lab-411/Stemfie-X/img/wheel_02_14_12_1.png

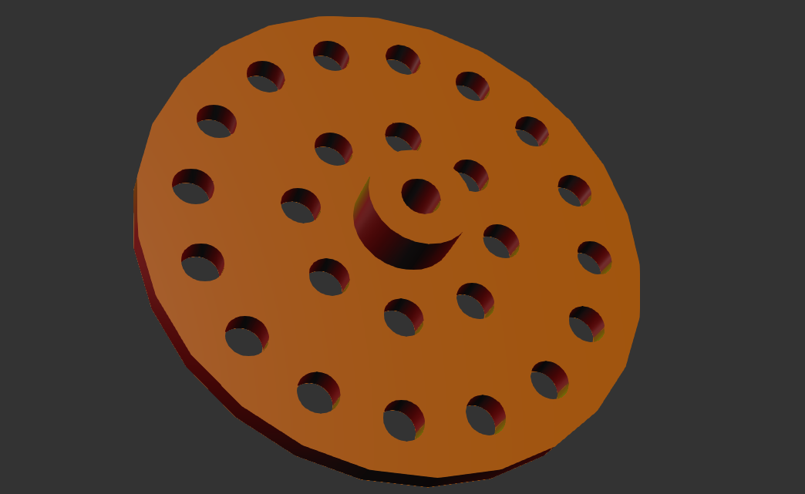
img/wheel_02_14_12_1.png
