lab-411/Stemfie-X/model/0210_most/img/most_06.png

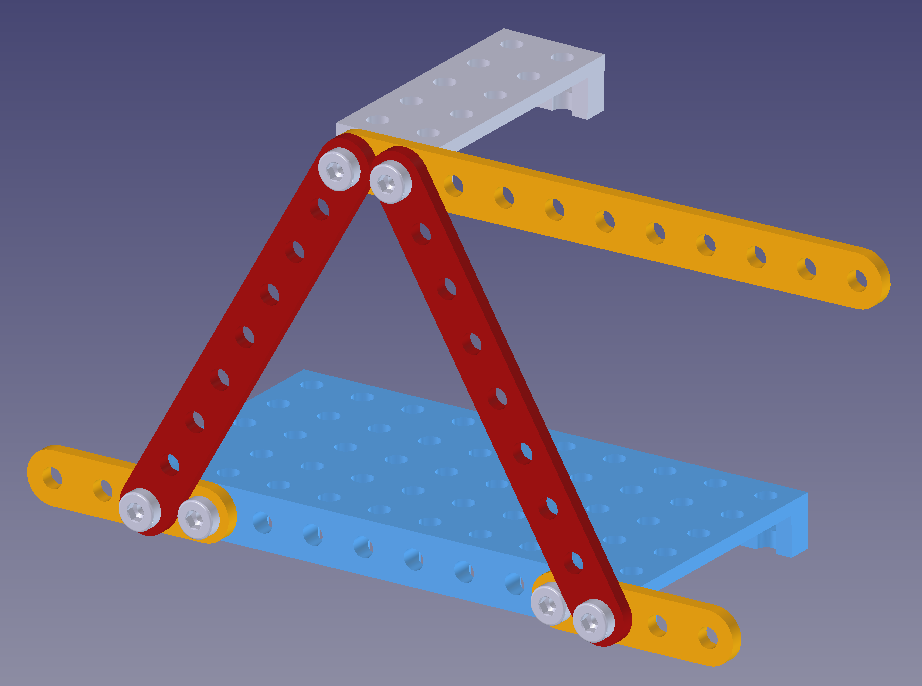
model/0210_most/img/most_06.png
