lab-411/Stemfie-X/model/0212_waren/img/zostava_02.png

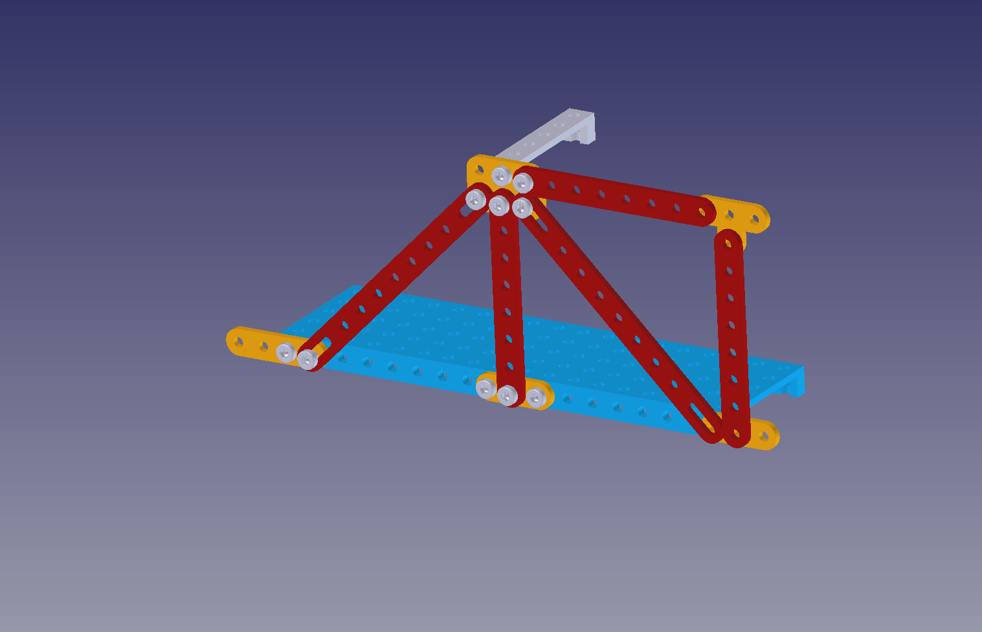
model/0212_waren/img/zostava_02.png
