lab-411/Stemfie-X/model/0215_mini_zeriav/img/2025-12-19_21-37.png

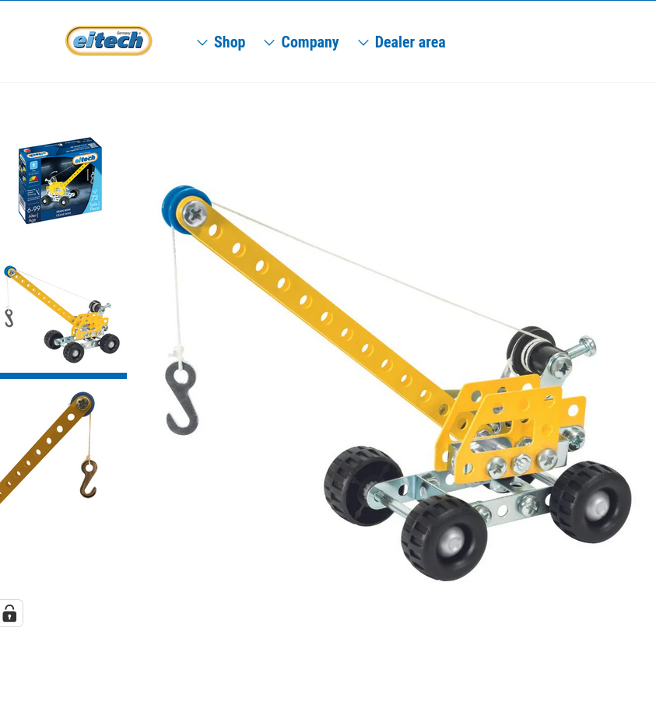
model/0215_mini_zeriav/img/2025-12-19_21-37.png
