lab-411/Stemfie-X/model/0215_mini_zeriav/img/diely_02.jpg

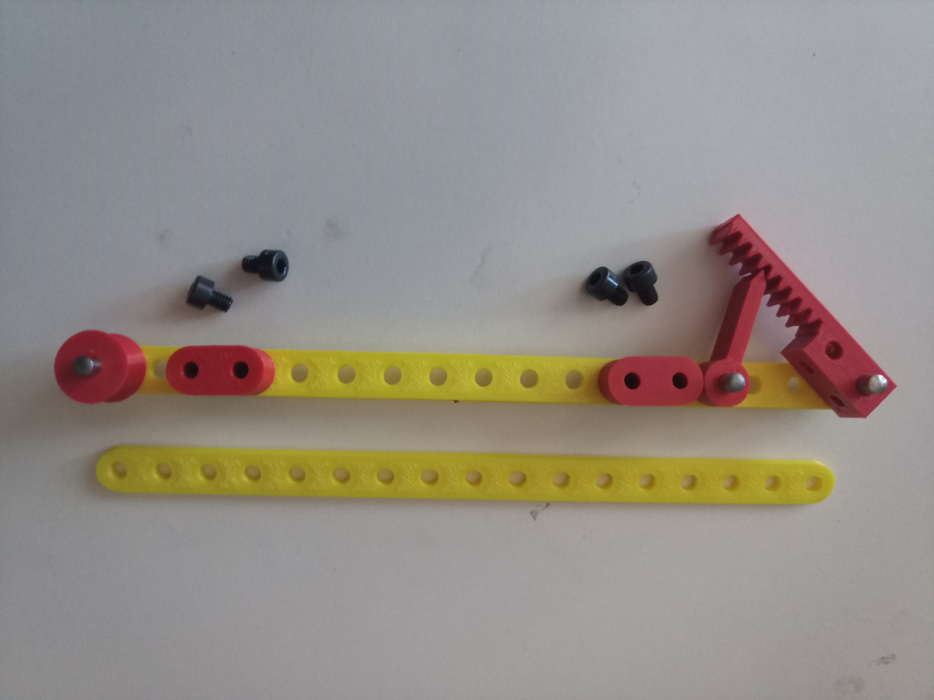
model/0215_mini_zeriav/img/diely_02.jpg
