lab-411/Stemfie-X/model/0215_mini_zeriav/img/IMG_20260729_085818_136.jpg

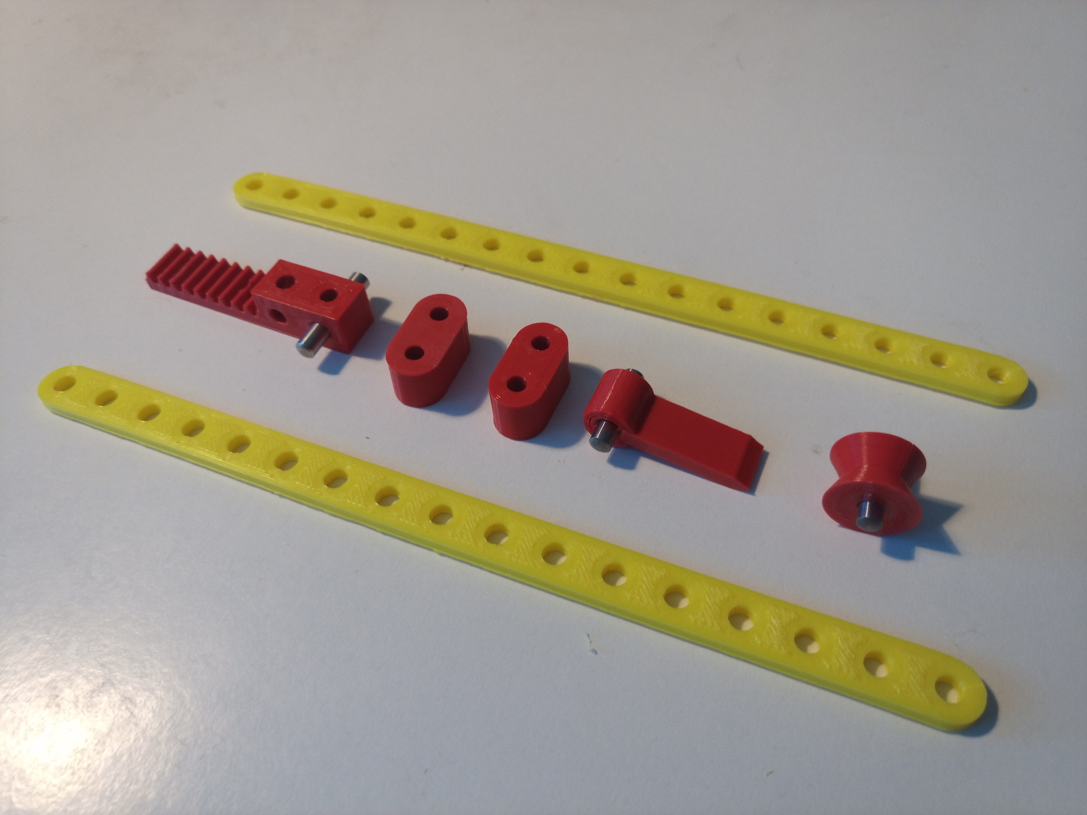
model/0215_mini_zeriav/img/IMG_20260729_085818_136.jpg
