lab-411/Stemfie-X/model/0215_mini_zeriav/img/IMG_20260729_090453_453.jpg

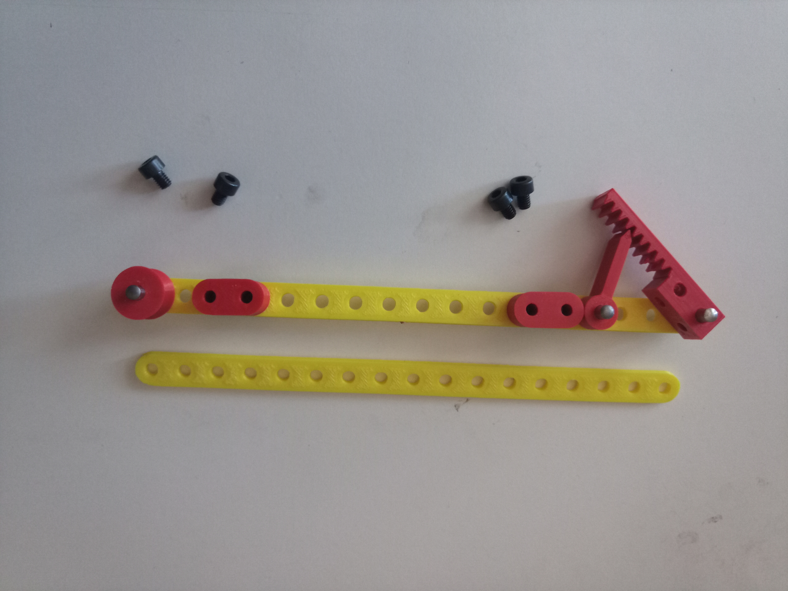
model/0215_mini_zeriav/img/IMG_20260729_090453_453.jpg
