lab-411/Stemfie-X/model/0215_mini_zeriav/img/IMG_20260730_194325_354.jpg

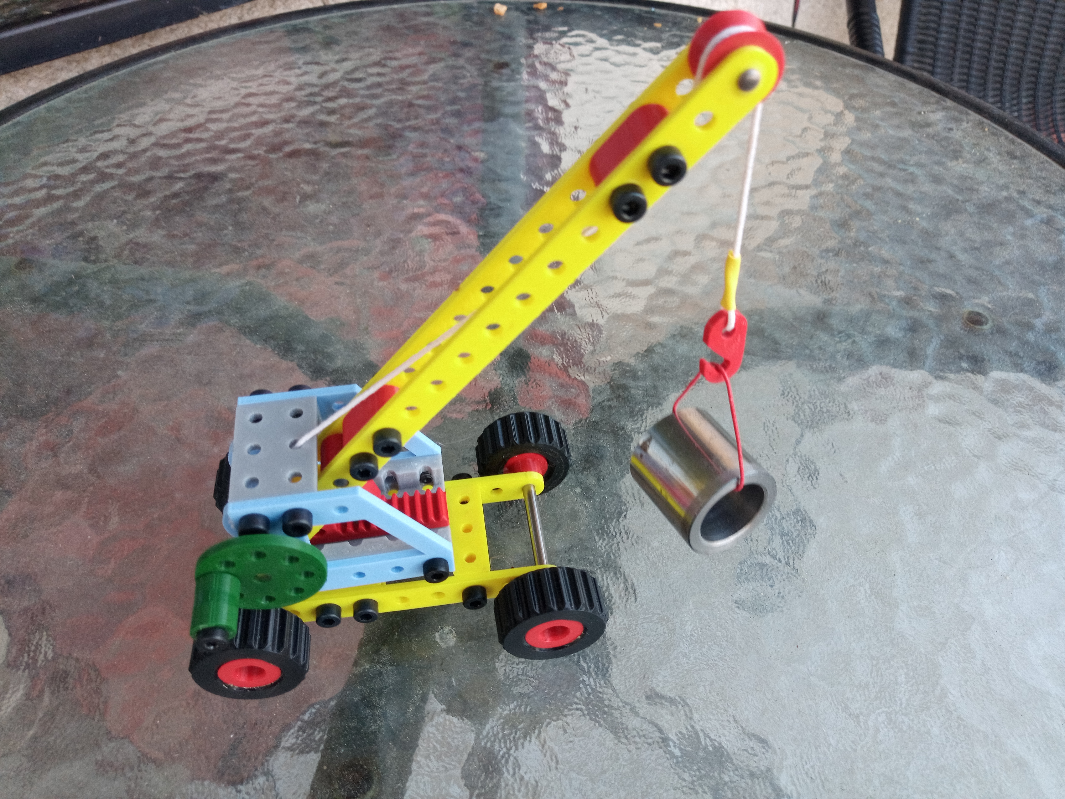
model/0215_mini_zeriav/img/IMG_20260730_194325_354.jpg
