lab-411/Stemfie-X/model/0215_mini_zeriav/img/IMG_20260730_194350_189.jpg

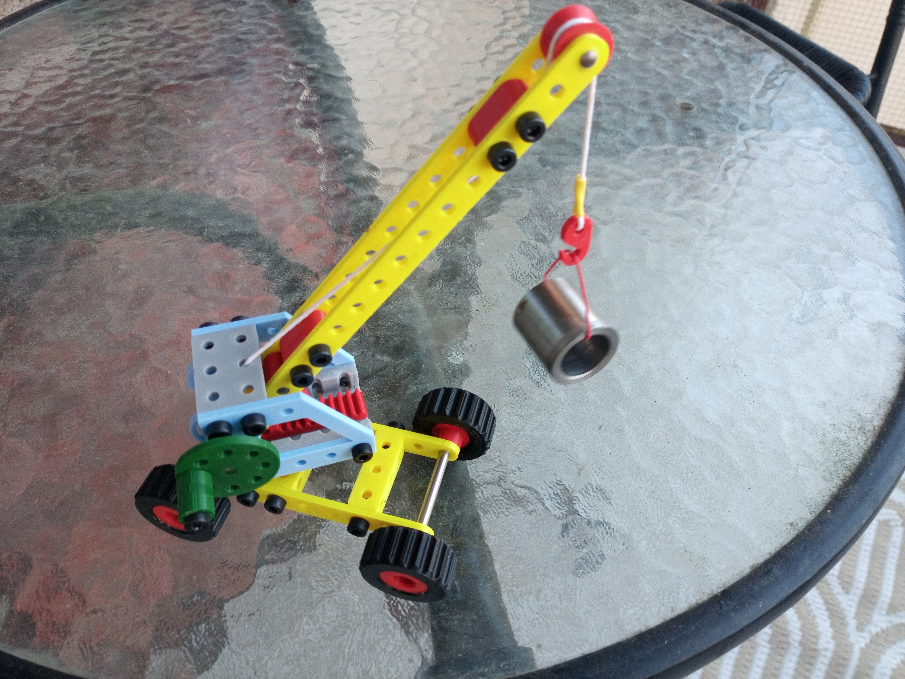
model/0215_mini_zeriav/img/IMG_20260730_194350_189.jpg
