lab-411/Stemfie-X/model/0215_mini_zeriav/img/img_sc_01.png

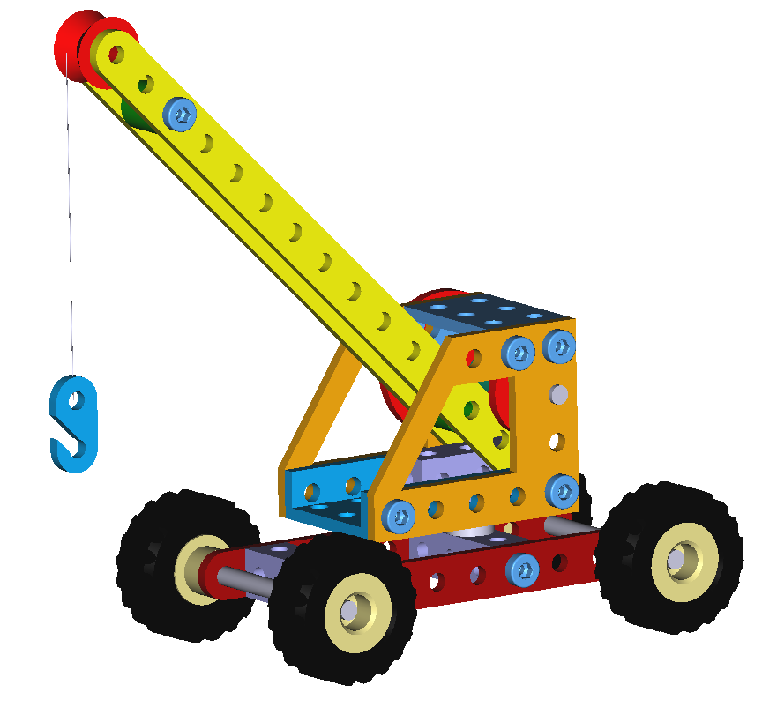
model/0215_mini_zeriav/img/img_sc_01.png
