lab-411/Stemfie-X/model/0215_mini_zeriav/img/img_sc_03.png

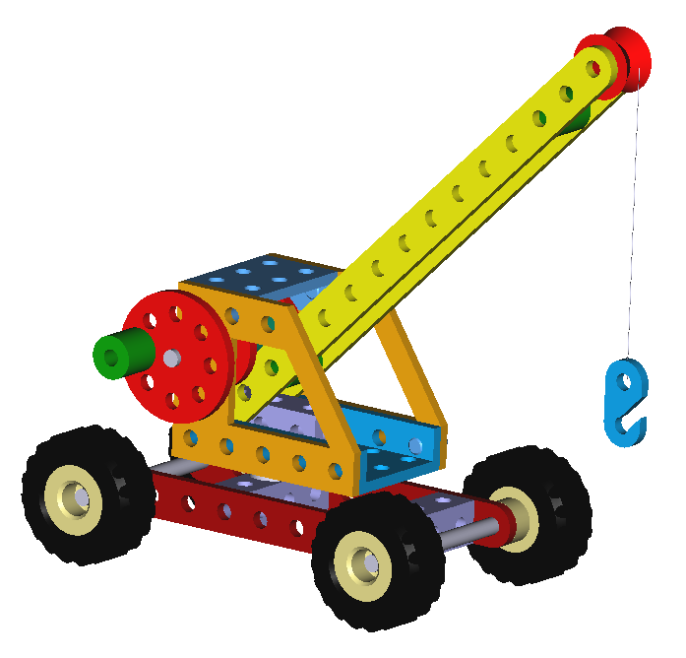
model/0215_mini_zeriav/img/img_sc_03.png
