lab-411/Stemfie-X/model/0215_mini_zeriav/img/img_zeriav_01.jpg

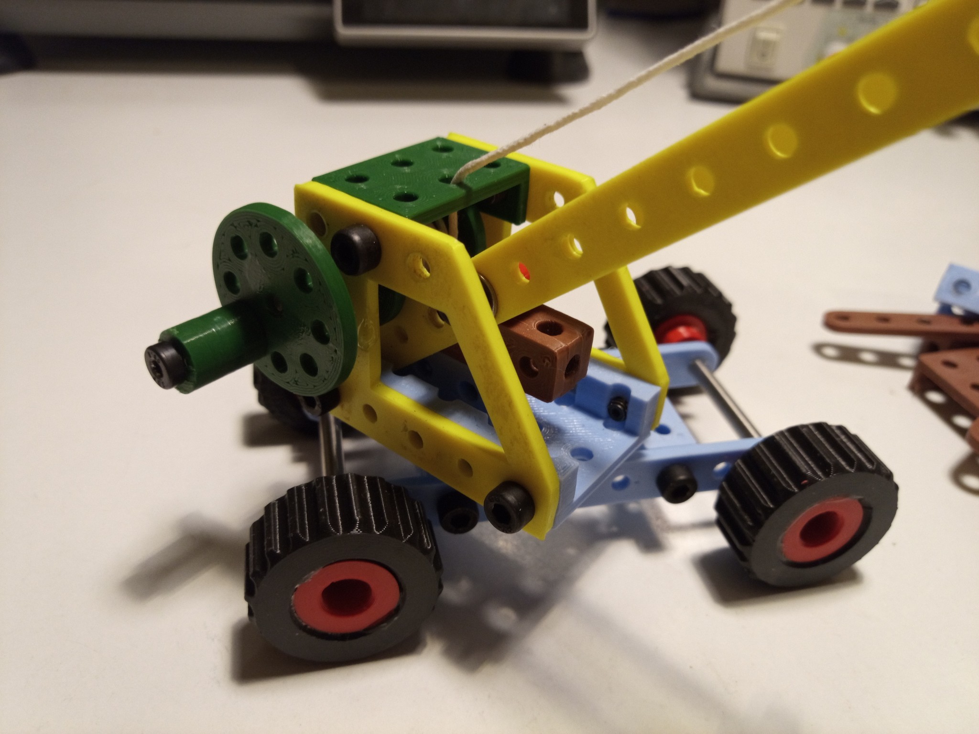
model/0215_mini_zeriav/img/img_zeriav_01.jpg
