lab-411/Stemfie-X/model/0215_mini_zeriav/img/kabina_03.png

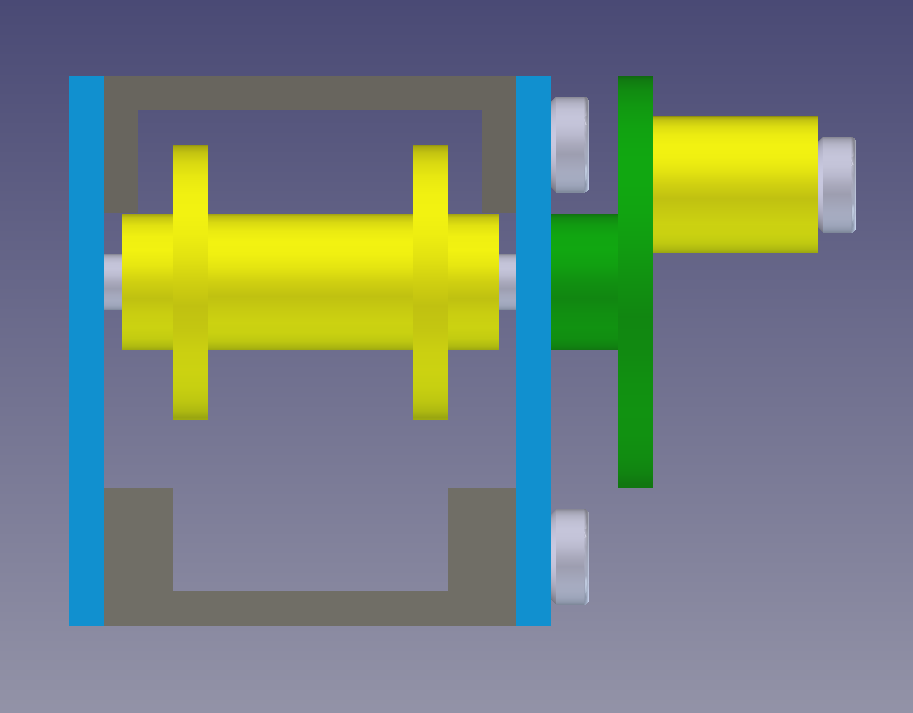
model/0215_mini_zeriav/img/kabina_03.png
