lab-411/Stemfie-X/model/0225_bobcat/img/img_04.png

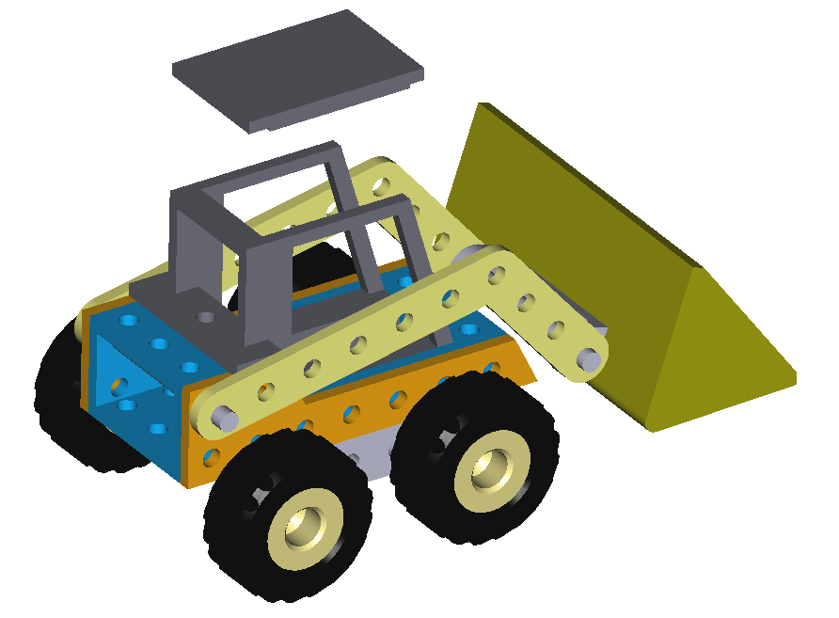
model/0225_bobcat/img/img_04.png
