lab-411/Stemfie-X/model/0225_bobcat_v02/img/IMG_20260118_134334_418.jpg

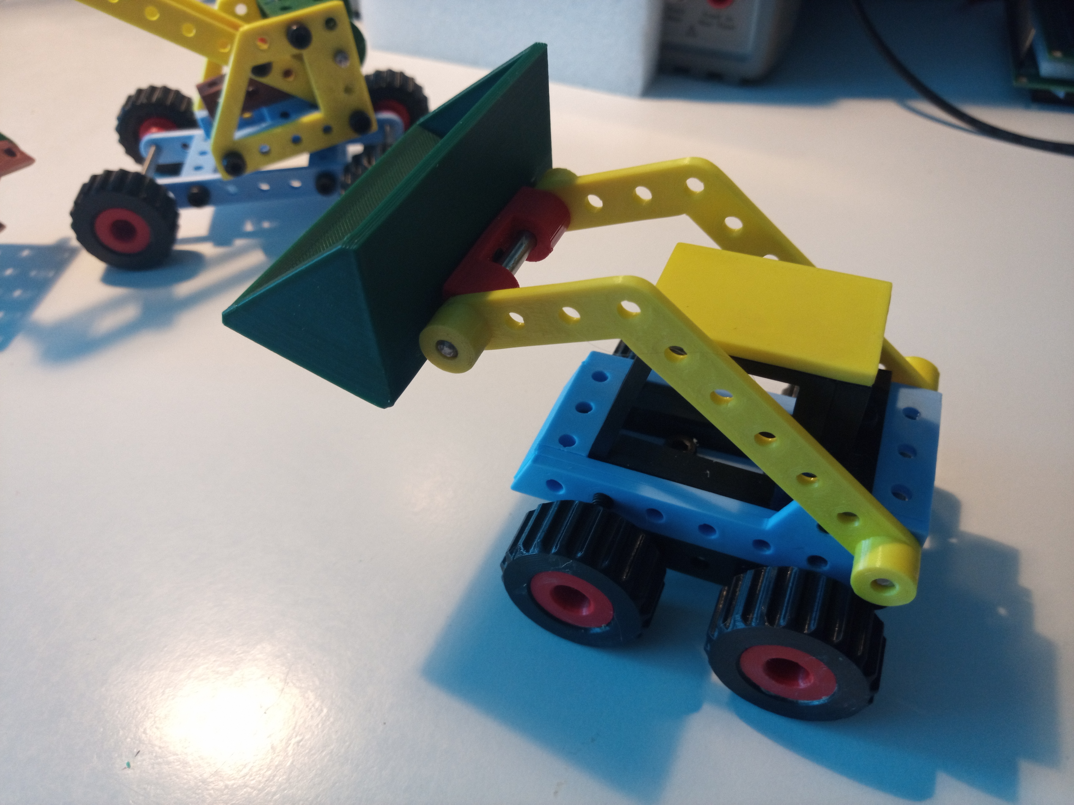
model/0225_bobcat_v02/img/IMG_20260118_134334_418.jpg
