lab-411/Stemfie-X/plantuml/aktivity.png

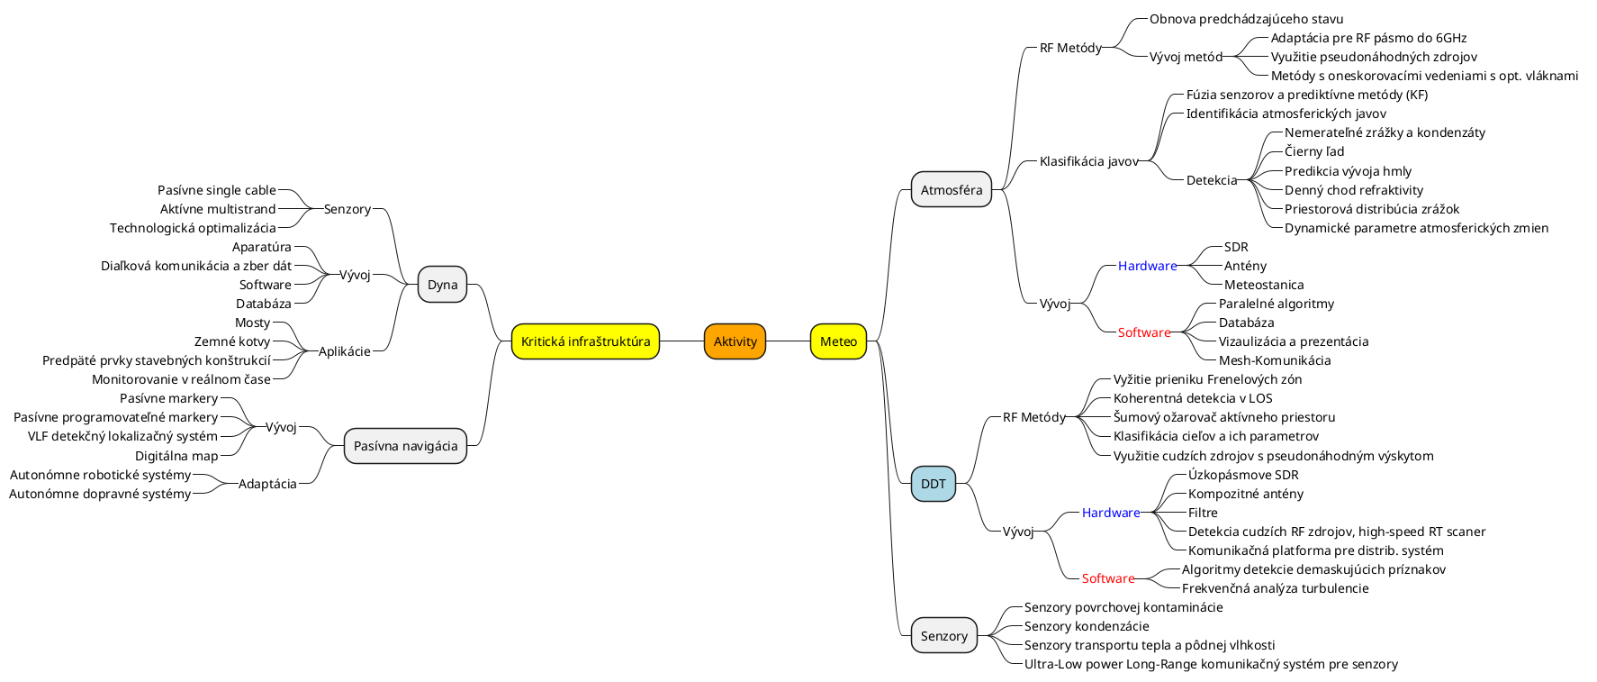
plantuml/aktivity.png
