lab-411/Stemfie-X/plantuml/kompetencie.png

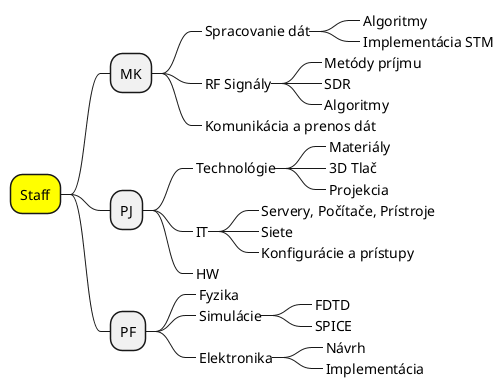
plantuml/kompetencie.png
