lab-411/Stemfie-X/src/0520b.png

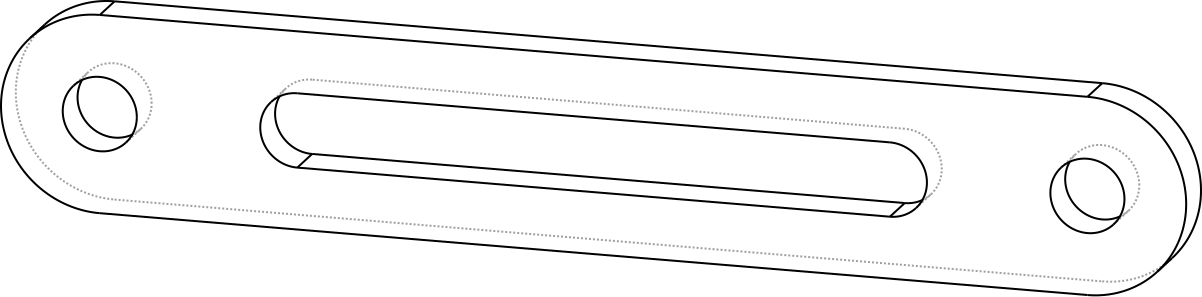
src/0520b.png
