lab-411/Stemfie-X/model/0225_bobcat/parts/user_P_03_24.step

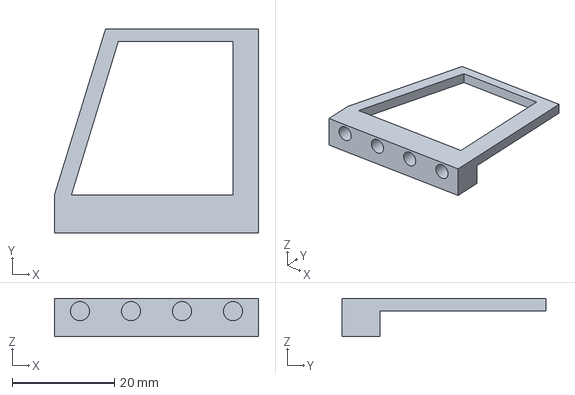
[picture p125: CAD file, 2026-01-18]
model/0225_bobcat/parts/user_P_03_24.step
40.0 x 40.0 x 7.50 mm
