lab-411/Stemfie-X/model/0225_bobcat_v02/parts/block_B_03.step

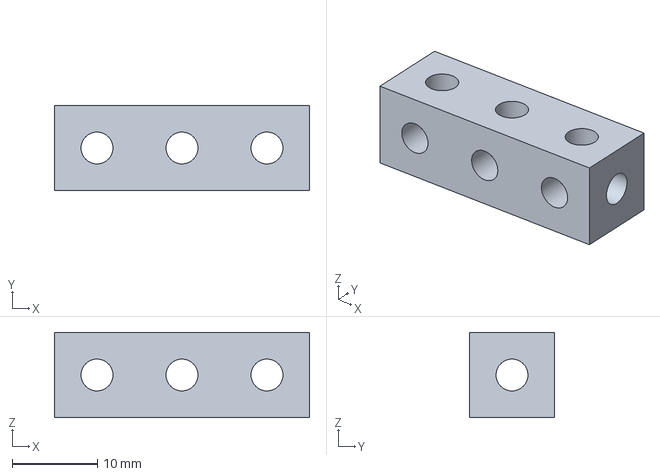
[picture p126: CAD file, 2026-01-18]
model/0225_bobcat_v02/parts/block_B_03.step
30.0 x 10.0 x 10.0 mm
