lab-411/Stemfie-X/model/1020_spirograf/parts/sp_gear_50.step

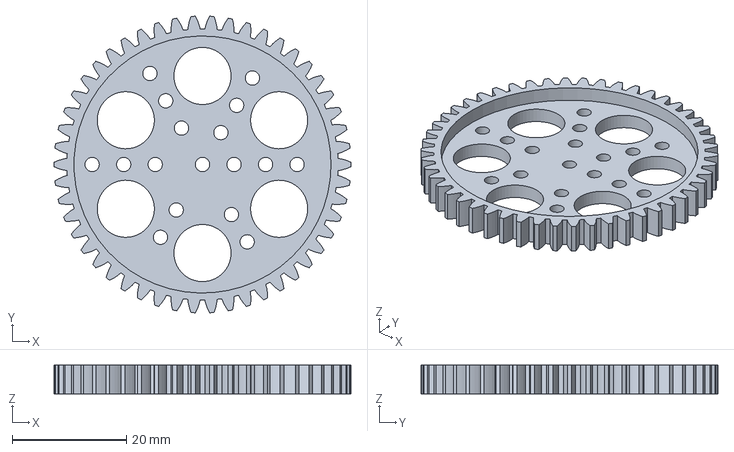
[picture p127: CAD file, 2026-01-18]
model/1020_spirograf/parts/sp_gear_50.step
52.0 x 51.9 x 5.00 mm
