lab-411/Stemfie-X/model/0210_most/parts/block_U_02_05_14_12.step

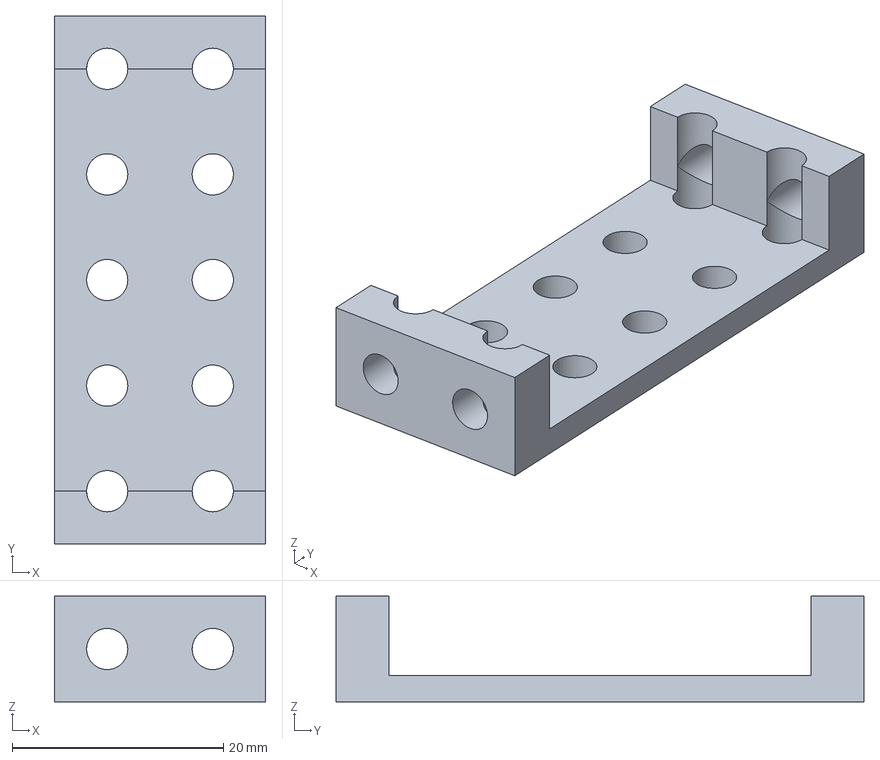
[picture p128: CAD file, 2025-12-20]
model/0210_most/parts/block_U_02_05_14_12.step
20.0 x 50.0 x 10.0 mm
