lab-411/Stemfie-X/model/0215_mini_zeriav/parts/wheel_B_02_14.step

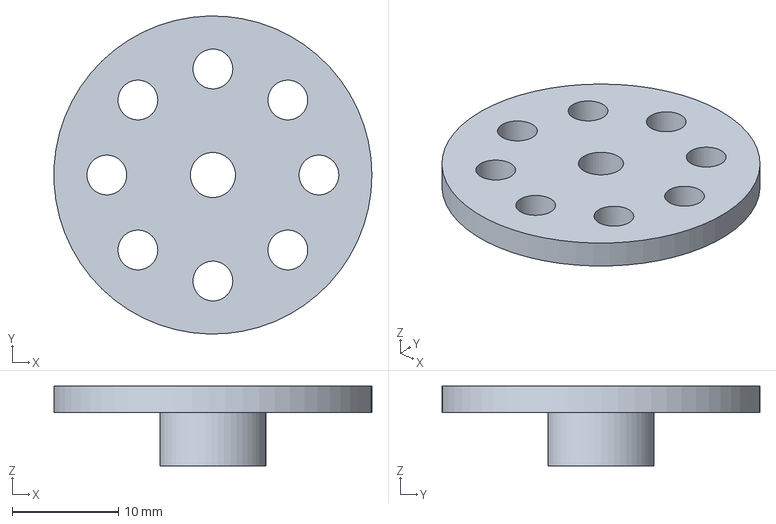
[picture p129: CAD file, 2026-07-30]
model/0215_mini_zeriav/parts/wheel_B_02_14.step
30.0 x 30.0 x 7.50 mm
