lab-411/Stemfie-X/model/0220_maly_mlyn/parts/brace_B_05.step

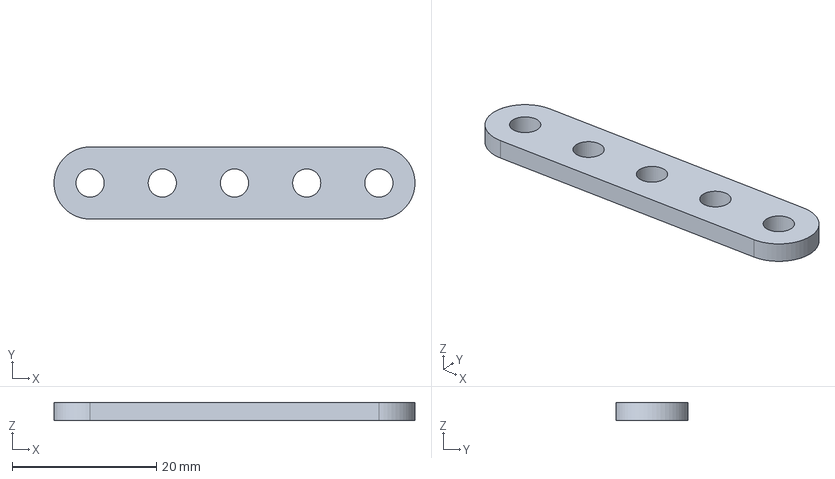
[picture p130: CAD file, 2026-01-04]
model/0220_maly_mlyn/parts/brace_B_05.step
50.0 x 10.0 x 2.50 mm
