lab-411/Stemfie-X/model/0225_bobcat/parts/user_Y_35_01.step

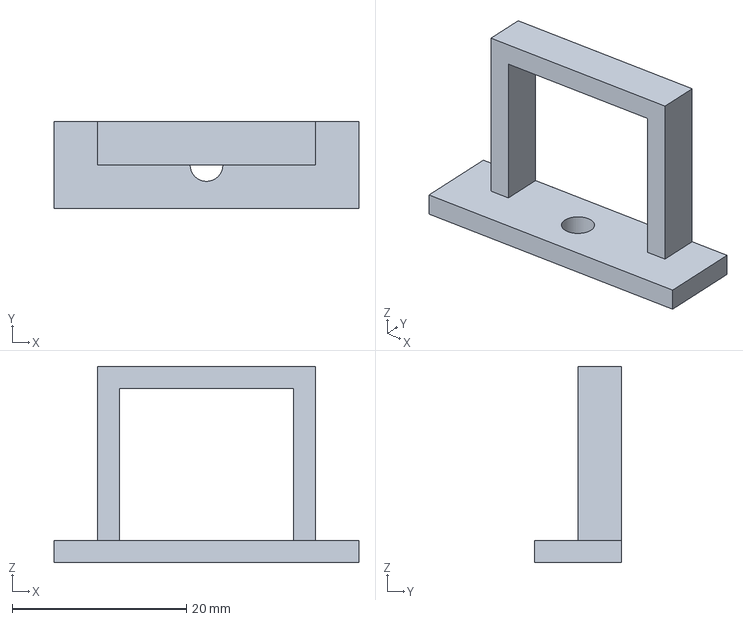
[picture p131: CAD file, 2026-01-18]
model/0225_bobcat/parts/user_Y_35_01.step
35.0 x 10.0 x 22.5 mm
