lab-411/Stemfie-X/model/1020_spirograf/parts/sp_base_90.step

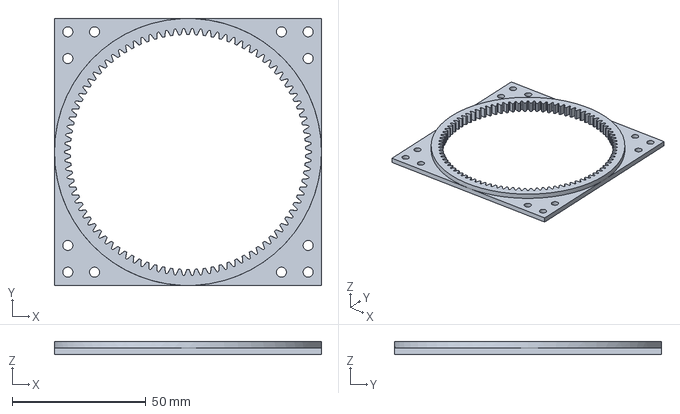
[picture p132: CAD file, 2026-01-18]
model/1020_spirograf/parts/sp_base_90.step
100.0 x 100.0 x 5.00 mm
