lab-411/Stemfie-X/model/0210_most/parts/brace_P_03_02_14.step

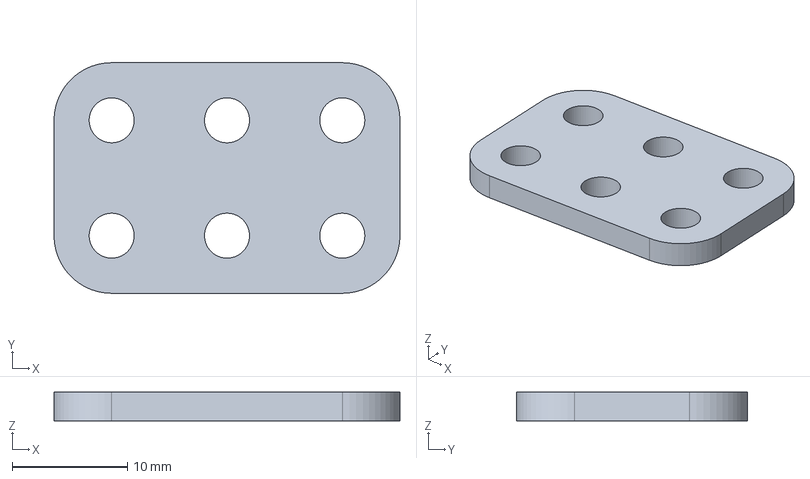
[picture p133: CAD file, 2025-12-20]
model/0210_most/parts/brace_P_03_02_14.step
30.0 x 20.0 x 2.50 mm
