lab-411/Stemfie-X/model/0215_mini_zeriav/parts/rameno.FCStd

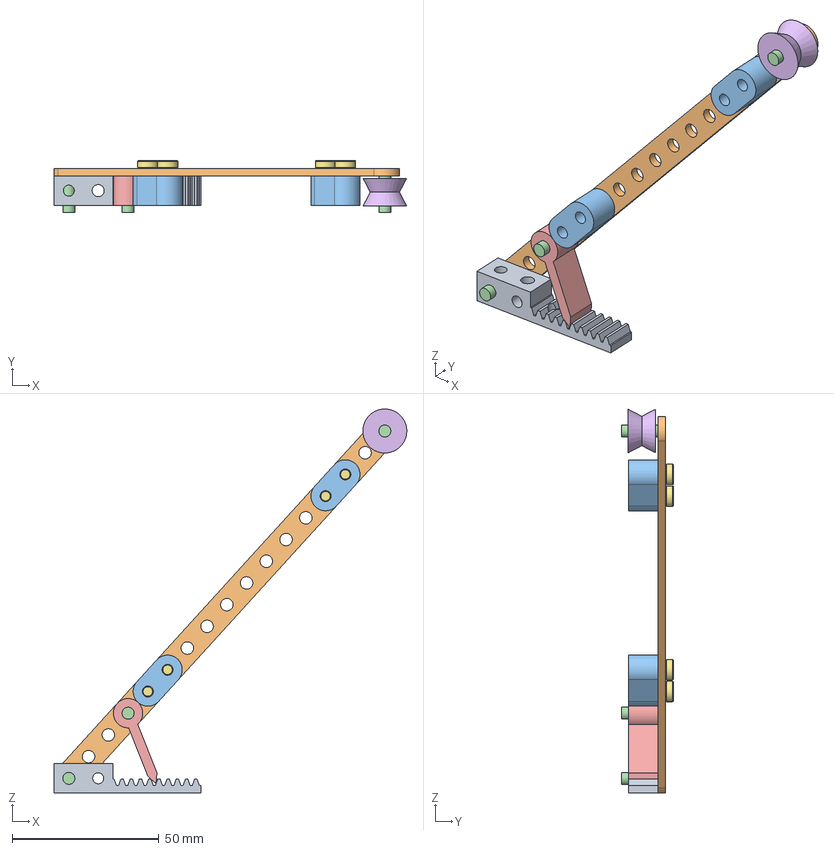
[picture p134: CAD file, 2026-07-30]
model/0215_mini_zeriav/parts/rameno.FCStd
120.2 x 17.8 x 130.8 mm
drziak
rameno
spojka x 2
os_15 x 3
podpera
kladka
M4x6-Screw x 4
