lab-411/Stemfie-X/model/0220_maly_mlyn/parts/brace_B_10.step

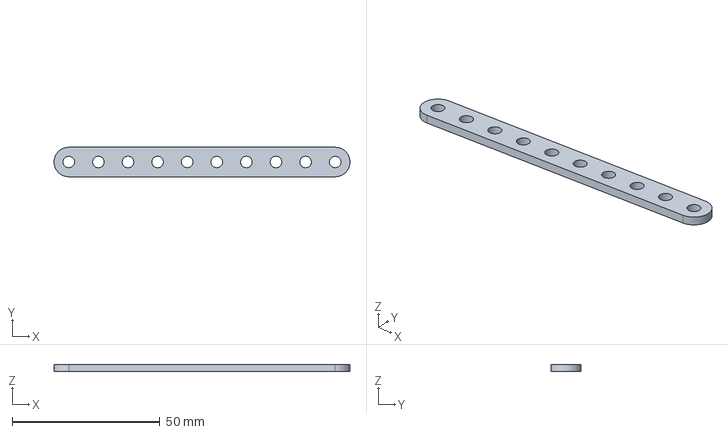
[picture p135: CAD file, 2026-01-04]
model/0220_maly_mlyn/parts/brace_B_10.step
100.0 x 10.0 x 2.50 mm
