lab-411/Stemfie-X/model/0225_bobcat_v02/parts/tire_T_01_03_15.step

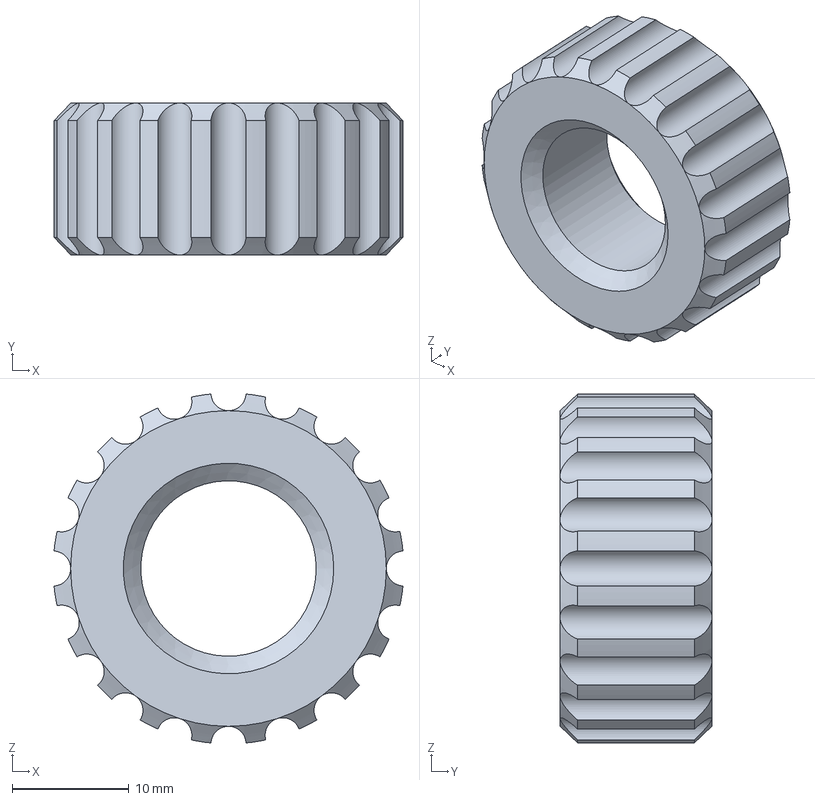
[picture p137: CAD file, 2026-01-18]
model/0225_bobcat_v02/parts/tire_T_01_03_15.step
29.9 x 13.0 x 29.9 mm
