lab-411/Stemfie-X/model/1020_spirograf/parts/sp_gear_65.step

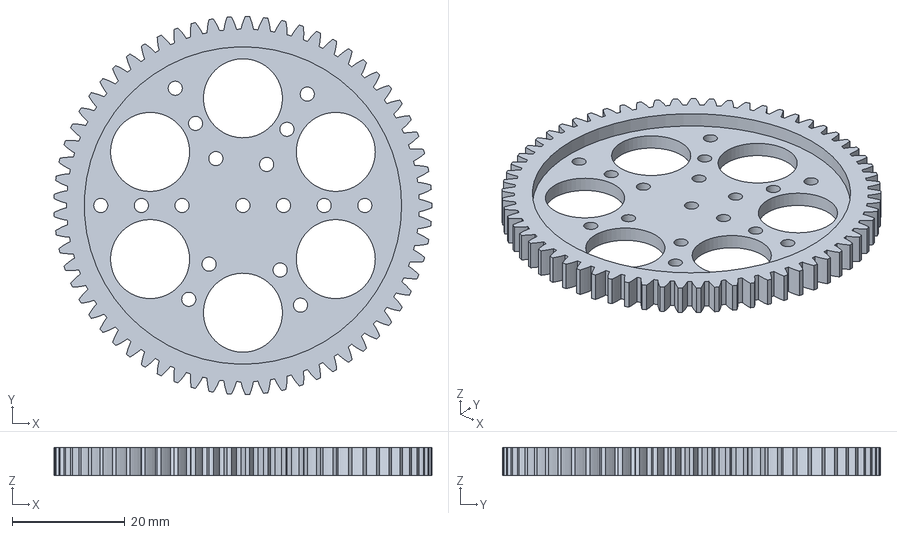
[picture p138: CAD file, 2026-01-18]
model/1020_spirograf/parts/sp_gear_65.step
67.0 x 67.0 x 5.00 mm
