lab-411/Stemfie-X/model/0212_waren/parts/brace_B_03_14.step

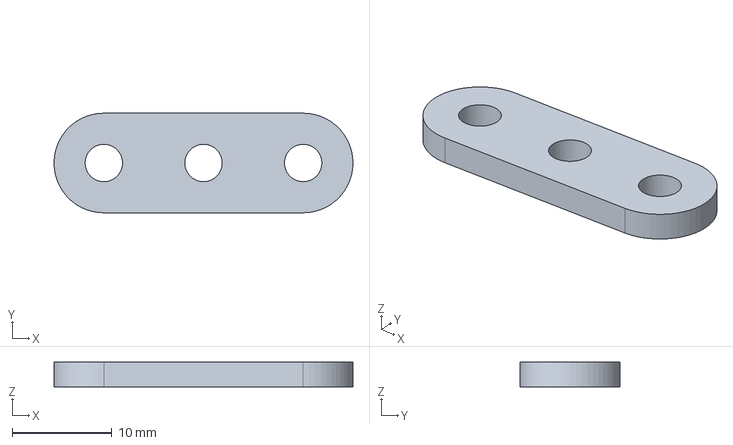
[picture p140: CAD file, 2026-08-03]
model/0212_waren/parts/brace_B_03_14.step
30.0 x 10.0 x 2.50 mm
