lab-411/Stemfie-X/model/0215_mini_zeriav/parts/rack_2.step

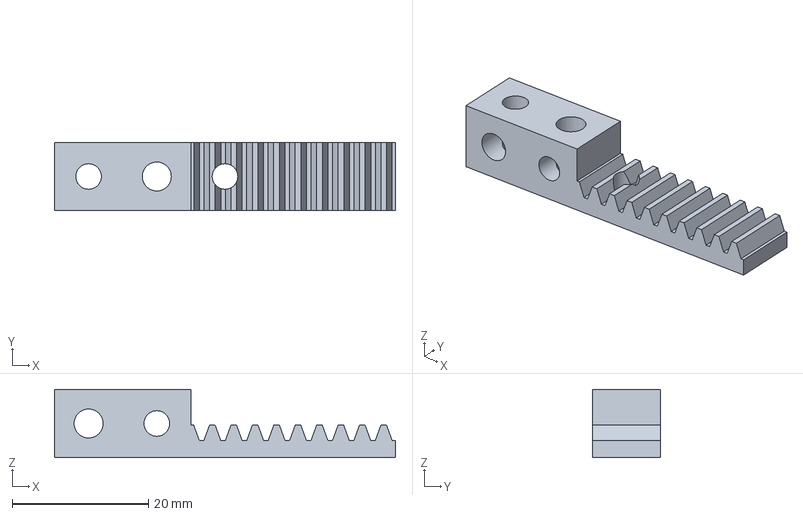
[picture p141: CAD file, 2026-07-30]
model/0215_mini_zeriav/parts/rack_2.step
50.0 x 10.0 x 10.0 mm
