lab-411/Stemfie-X/model/0220_maly_mlyn/parts/brace_A_03_14_06_112.step

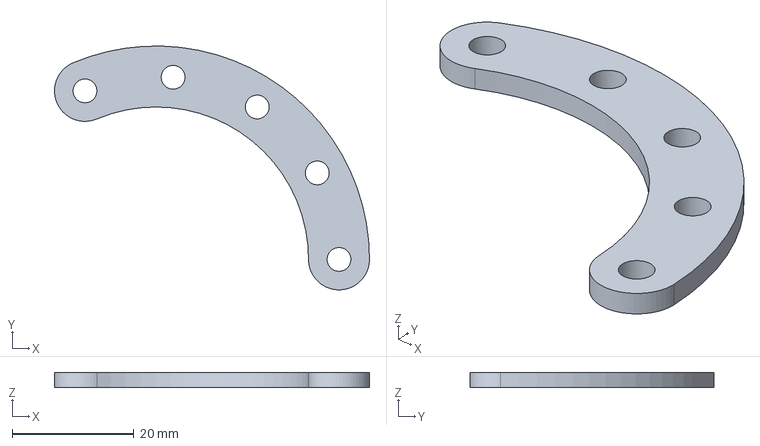
[picture p142: CAD file, 2026-01-04]
model/0220_maly_mlyn/parts/brace_A_03_14_06_112.step
51.7 x 40.0 x 2.50 mm
