lab-411/Stemfie-X/model/0225_bobcat_v02/parts/user_X_35_01.step

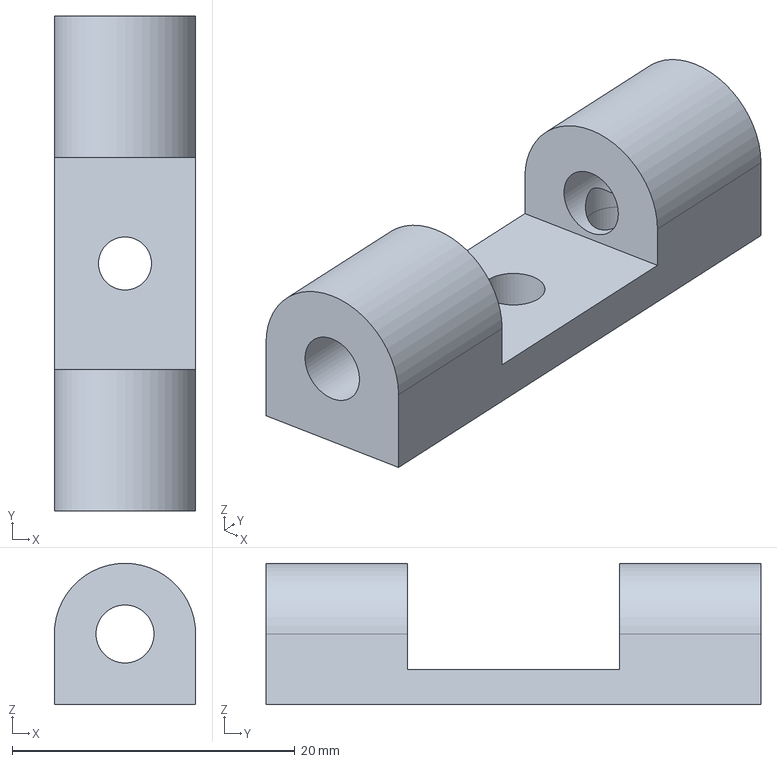
[picture p143: CAD file, 2026-01-18]
model/0225_bobcat_v02/parts/user_X_35_01.step
10.0 x 35.0 x 10.0 mm
