lab-411/Stemfie-X/model/0210_most/parts/brace_B_09_14.step

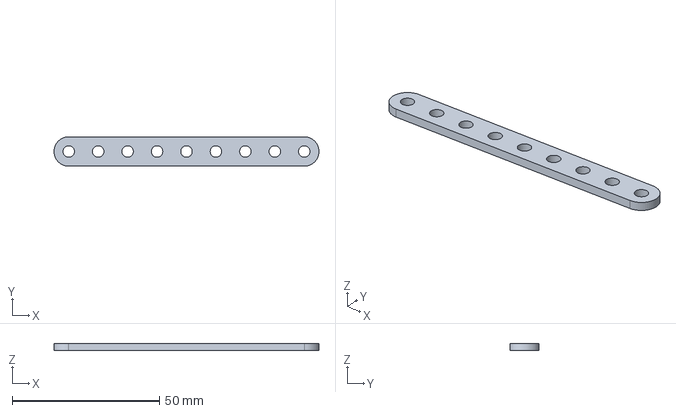
[picture p144: CAD file, 2025-12-20]
model/0210_most/parts/brace_B_09_14.step
90.0 x 10.0 x 2.50 mm
