lab-411/Stemfie-X/model/0215_mini_zeriav/parts/wheel_A_15_14.step

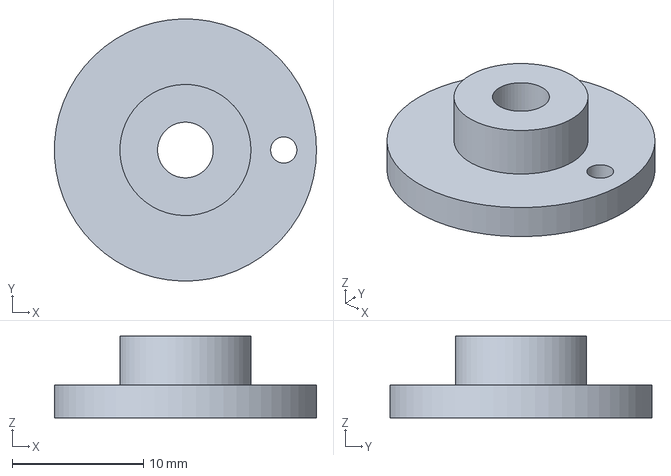
[picture p145: CAD file, 2026-07-30]
model/0215_mini_zeriav/parts/wheel_A_15_14.step
20.0 x 20.0 x 6.25 mm
