lab-411/Stemfie-X/model/0220_maly_mlyn/parts/wheel_B_12_12.step

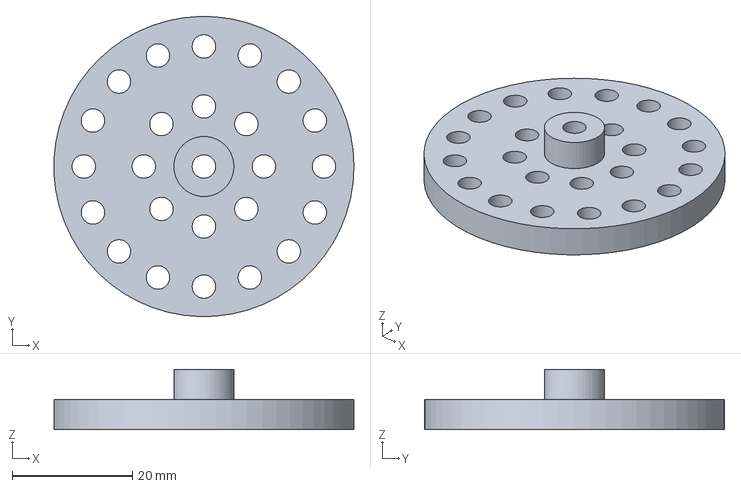
[picture p146: CAD file, 2026-01-04]
model/0220_maly_mlyn/parts/wheel_B_12_12.step
50.0 x 50.0 x 10.0 mm
