lab-411/Stemfie-X/model/0212_waren/parts/brace_T_03_02.step

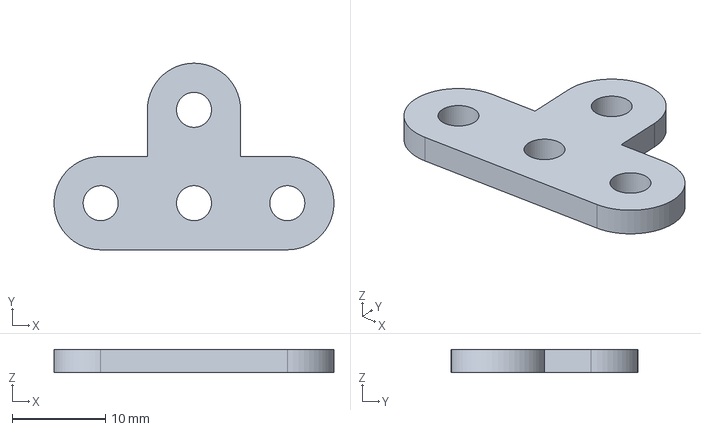
[picture p147: CAD file, 2026-08-03]
model/0212_waren/parts/brace_T_03_02.step
30.0 x 20.0 x 2.50 mm
