lab-411/Stemfie-X/model/0215_mini_zeriav/parts/axis_5.step

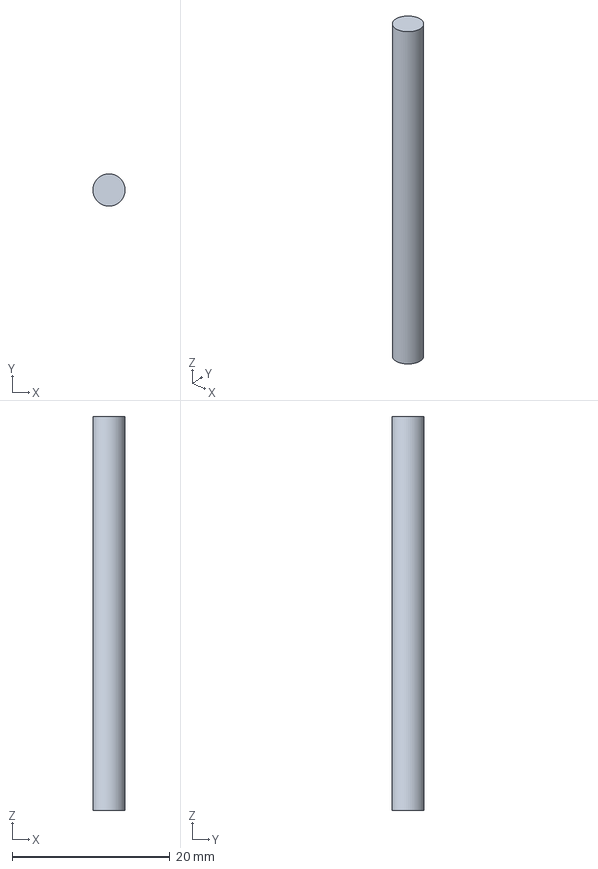
[picture p148: CAD file, 2026-07-30]
model/0215_mini_zeriav/parts/axis_5.step
4.10 x 4.10 x 50.0 mm
