lab-411/Stemfie-X/model/0220_maly_mlyn/parts/pull_B_12.step

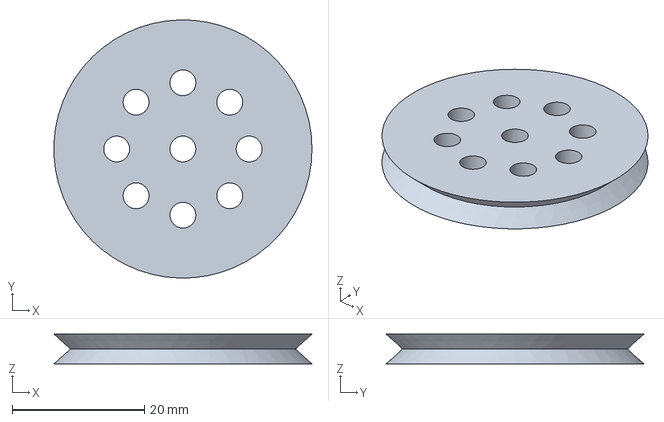
[picture p149: CAD file, 2026-01-04]
model/0220_maly_mlyn/parts/pull_B_12.step
39.0 x 39.0 x 4.50 mm
