lab-411/Stemfie-X/model/0212_waren/parts/block_H_05_05_14_12_02_02.step

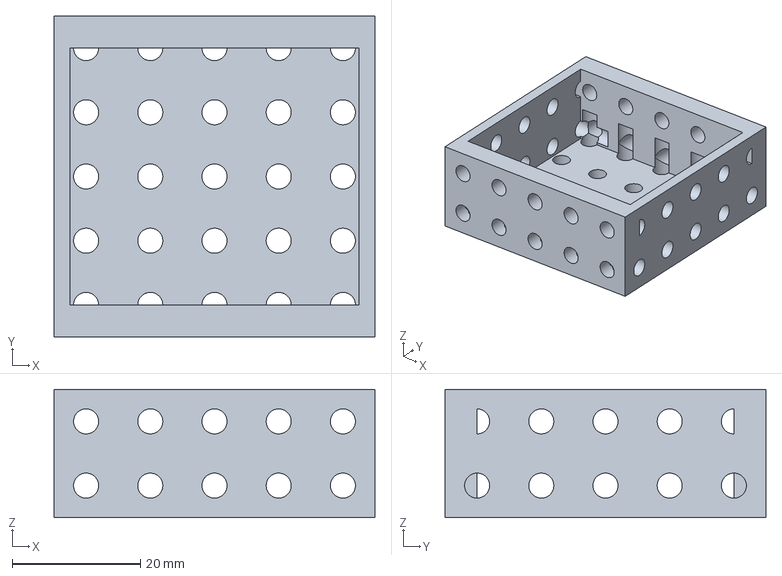
[picture p150: CAD file, 2025-12-20]
model/0212_waren/parts/block_H_05_05_14_12_02_02.step
50.0 x 50.0 x 20.0 mm
