lab-411/Stemfie-X/model/0215_mini_zeriav/parts/base_C_01_15.step

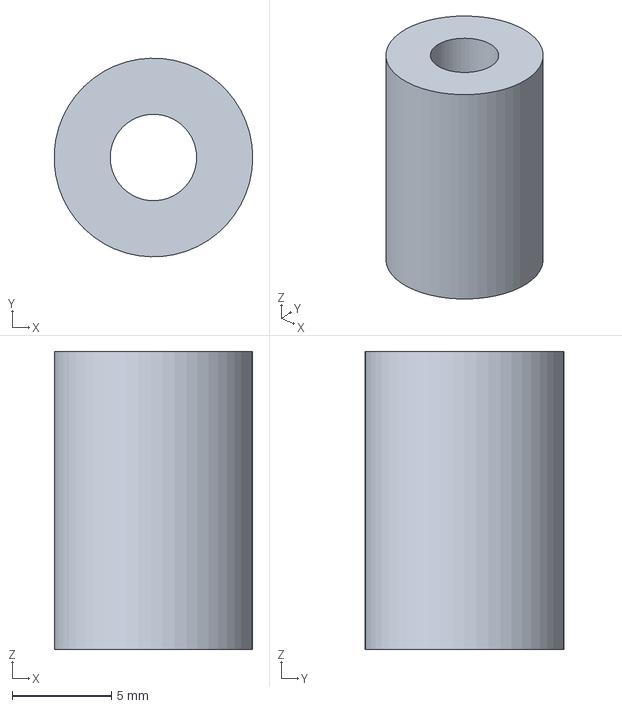
[picture p151: CAD file, 2026-07-30]
model/0215_mini_zeriav/parts/base_C_01_15.step
9.99 x 10.00 x 15.0 mm
