lab-411/Stemfie-X/model/0225_bobcat/parts/user_S_20_40.step

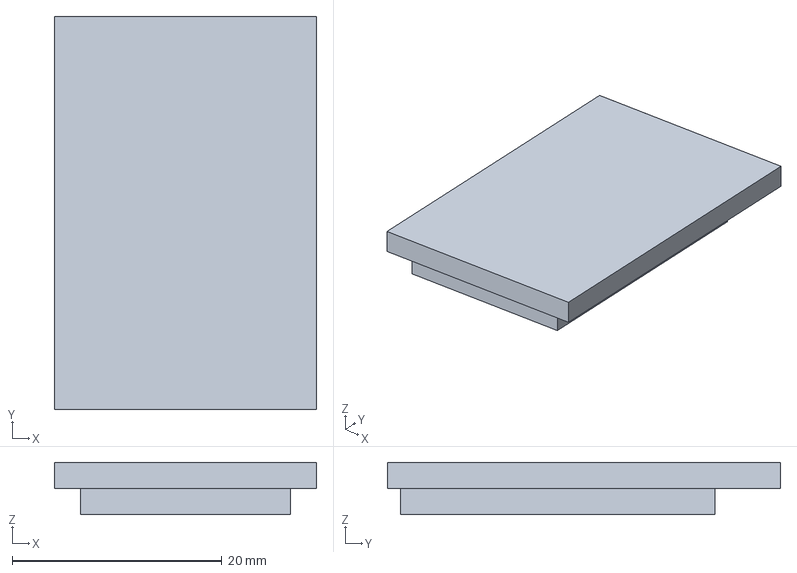
[picture p152: CAD file, 2026-01-18]
model/0225_bobcat/parts/user_S_20_40.step
25.0 x 37.5 x 5.00 mm
