lab-411/Stemfie-X/model/0225_bobcat_v02/parts/user_S_32_10.step

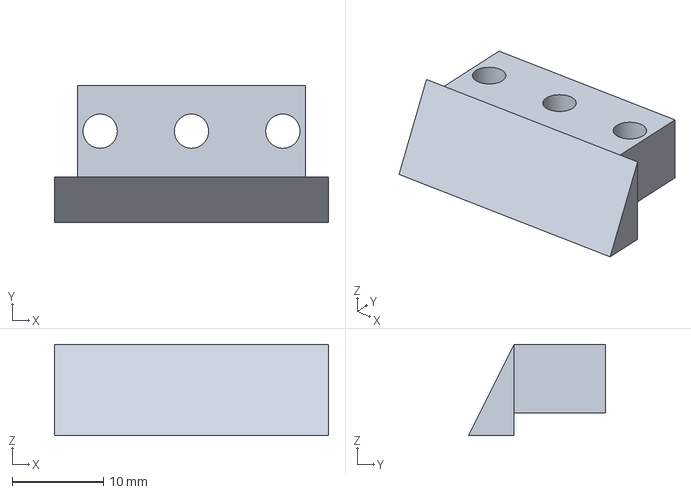
[picture p153: CAD file, 2026-01-18]
model/0225_bobcat_v02/parts/user_S_32_10.step
30.0 x 15.0 x 10.0 mm
