lab-411/Stemfie-X/model/0215_mini_zeriav/parts/tire_D_01_03_15.step

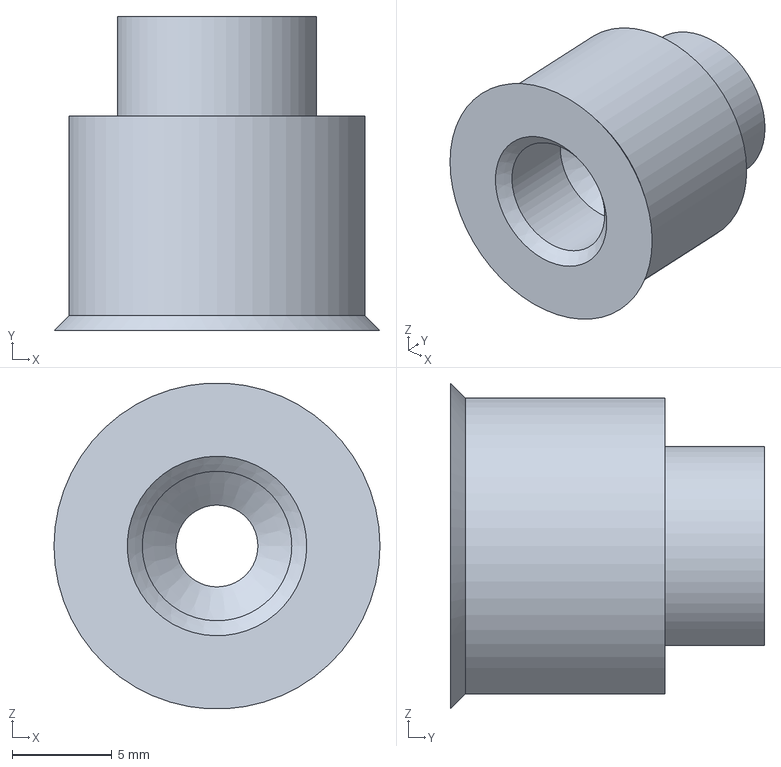
[picture p154: CAD file, 2026-07-30]
model/0215_mini_zeriav/parts/tire_D_01_03_15.step
16.4 x 15.8 x 16.3 mm
