lab-411/Stemfie-X/model/0225_bobcat/parts/block_X_07_04.step

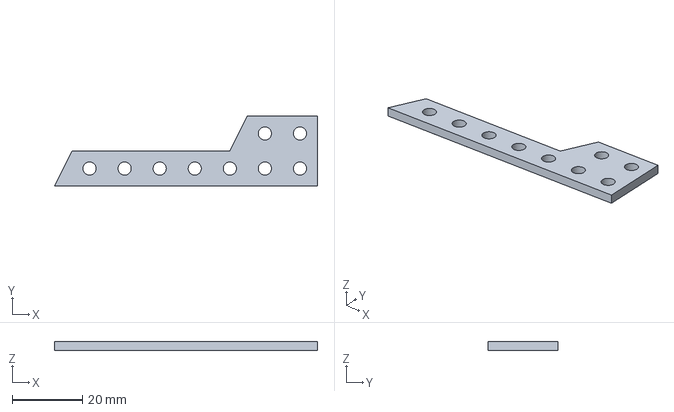
[picture p155: CAD file, 2026-01-18]
model/0225_bobcat/parts/block_X_07_04.step
75.0 x 20.0 x 2.50 mm
