lab-411/Stemfie-X/model/0212_waren/parts/block_U_09_05_14_12.step

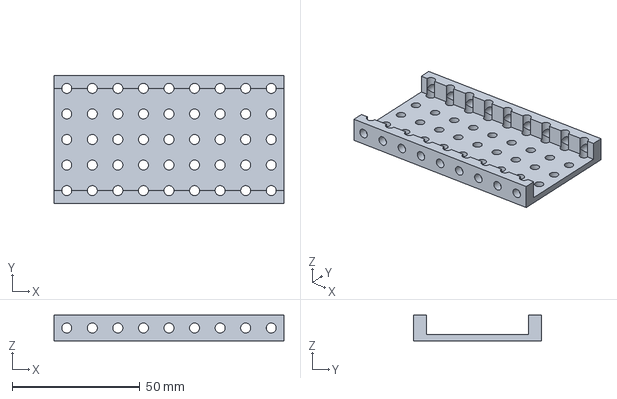
[picture p156: CAD file, 2025-12-20]
model/0212_waren/parts/block_U_09_05_14_12.step
90.0 x 50.0 x 10.0 mm
