lab-411/Stemfie-X/model/0215_mini_zeriav/parts/brace_B_17_14.step

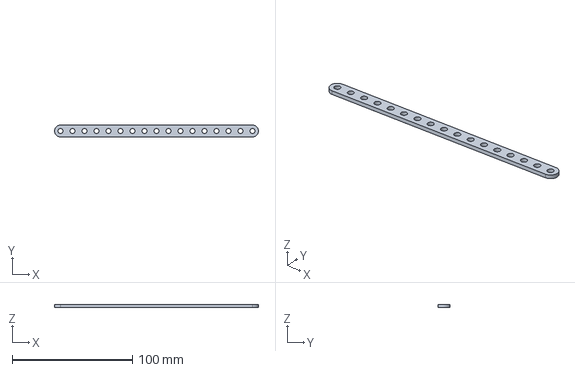
[picture p157: CAD file, 2026-07-30]
model/0215_mini_zeriav/parts/brace_B_17_14.step
170.0 x 10.0 x 2.50 mm
