lab-411/Stemfie-X/model/0215_mini_zeriav/parts/axis_60.step

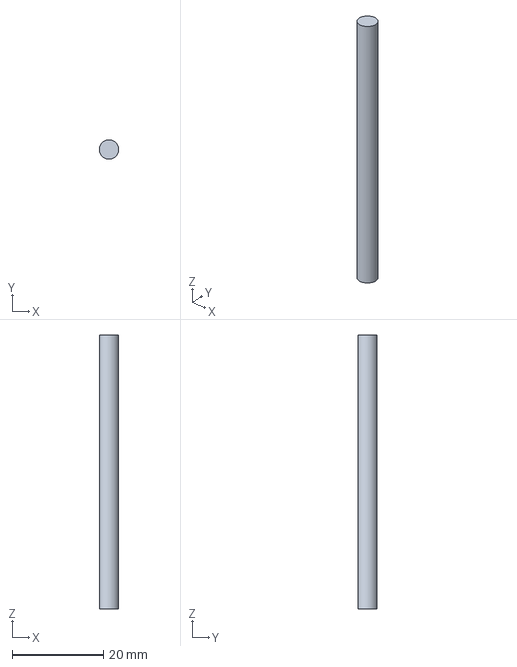
[picture p158: CAD file, 2026-07-30]
model/0215_mini_zeriav/parts/axis_60.step
4.25 x 4.25 x 60.0 mm
