lab-411/Stemfie-X/model/0225_bobcat/parts/user_R_35_01.step

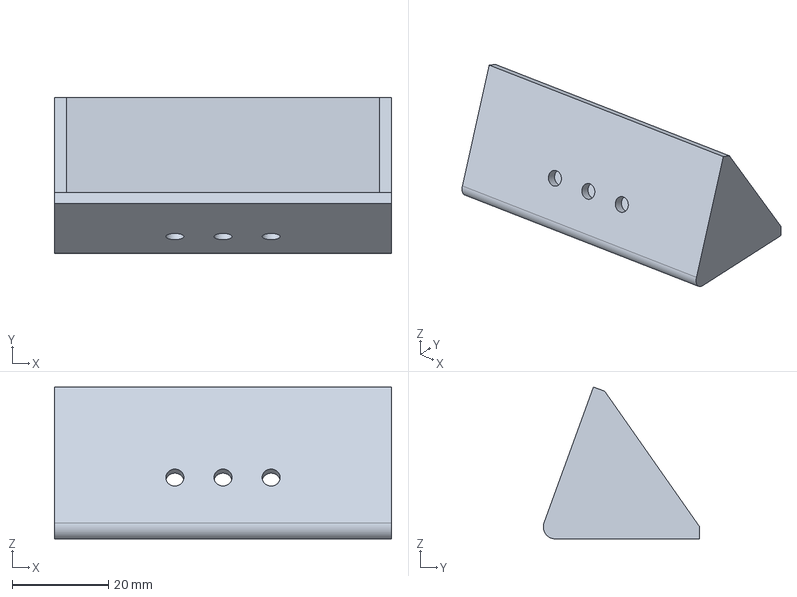
[picture p159: CAD file, 2026-01-18]
model/0225_bobcat/parts/user_R_35_01.step
70.0 x 32.5 x 31.5 mm
