lab-411/Stemfie-X/model/0215_mini_zeriav/parts/pulley_A_15.step

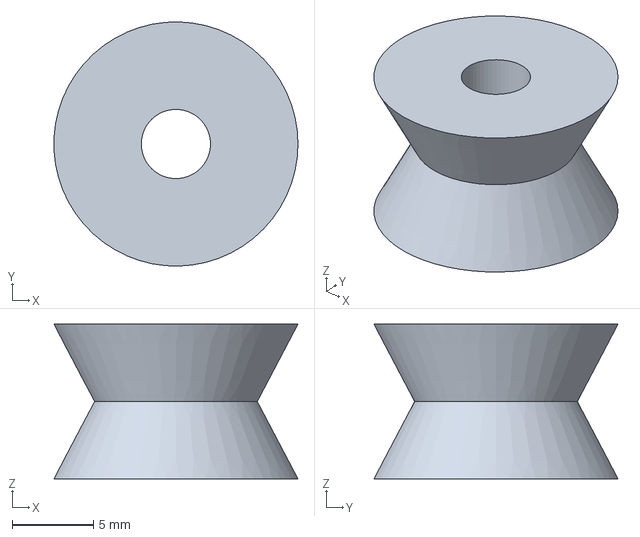
[picture p160: CAD file, 2026-07-30]
model/0215_mini_zeriav/parts/pulley_A_15.step
15.0 x 15.0 x 9.50 mm
