lab-411/Stemfie-X/model/0215_mini_zeriav/parts/block_B_03_02_01.step

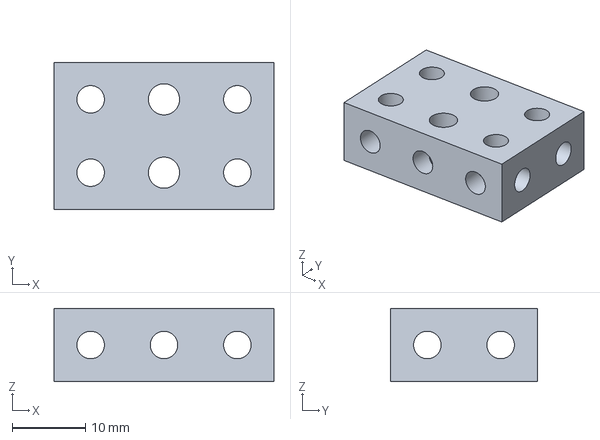
[picture p161: CAD file, 2026-07-30]
model/0215_mini_zeriav/parts/block_B_03_02_01.step
30.0 x 20.0 x 10.0 mm
