lab-411/Stemfie-X/model/0215_mini_zeriav/parts/podvozok.FCStd

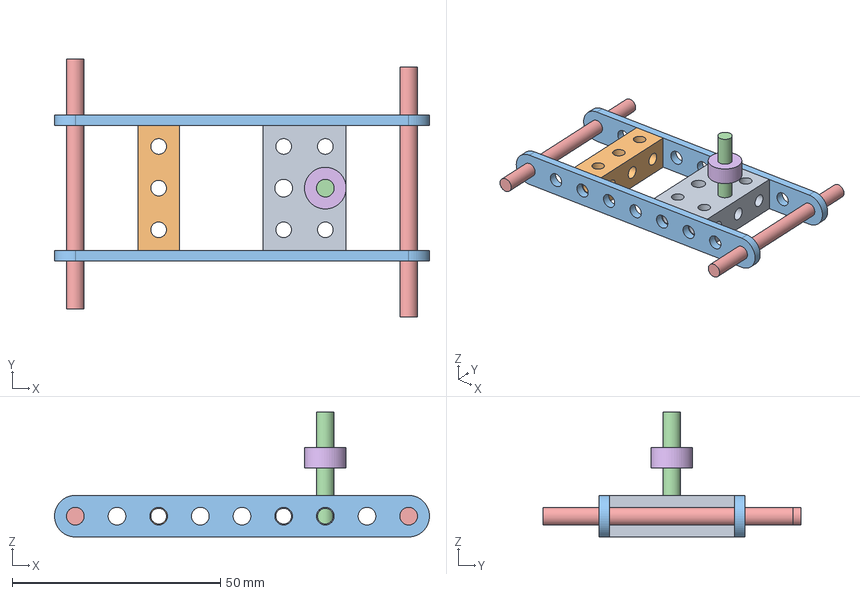
[picture p162: CAD file, 2026-07-30]
model/0215_mini_zeriav/parts/podvozok.FCStd
90.0 x 61.9 x 30.0 mm
nosnik_zadny
nosnik_predny
bocnica x 2
os_30
os_60 x 2
vymedzenie
