lab-411/Stemfie-X/model/0215_mini_zeriav/parts/axis_15.step

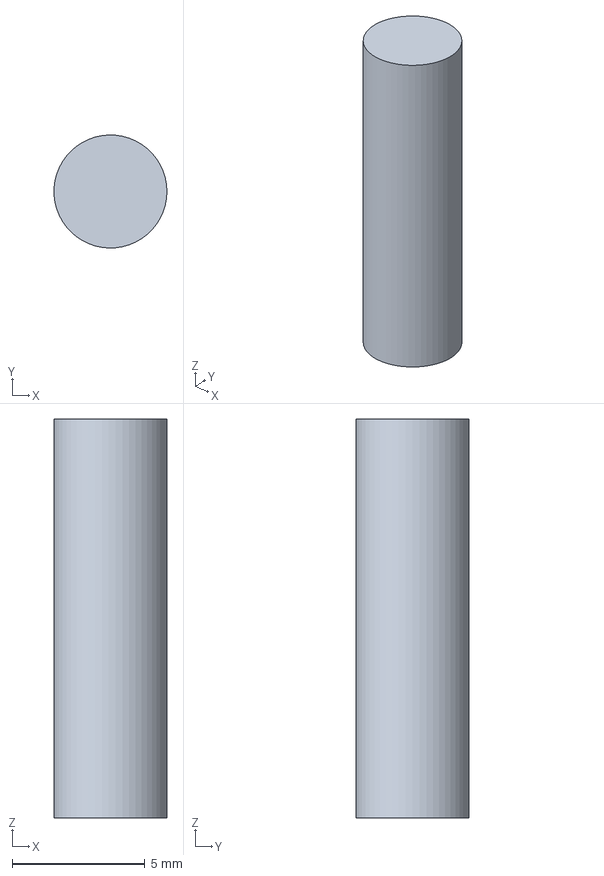
[picture p163: CAD file, 2026-07-30]
model/0215_mini_zeriav/parts/axis_15.step
4.25 x 4.25 x 15.0 mm
