lab-411/Stemfie-X/model/0215_mini_zeriav/parts/brace_B_02_01.step

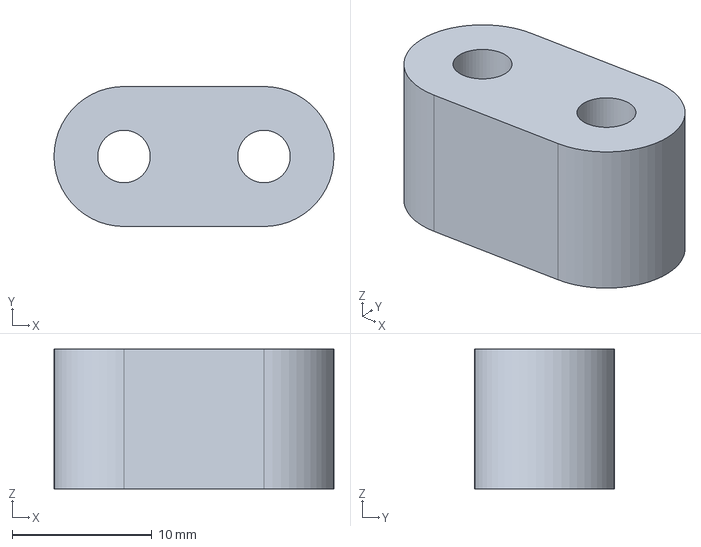
[picture p164: CAD file, 2026-07-30]
model/0215_mini_zeriav/parts/brace_B_02_01.step
20.0 x 10.0 x 10.0 mm
