lab-411/Stemfie-X/model/0215_mini_zeriav/parts/block_U_05_03.step

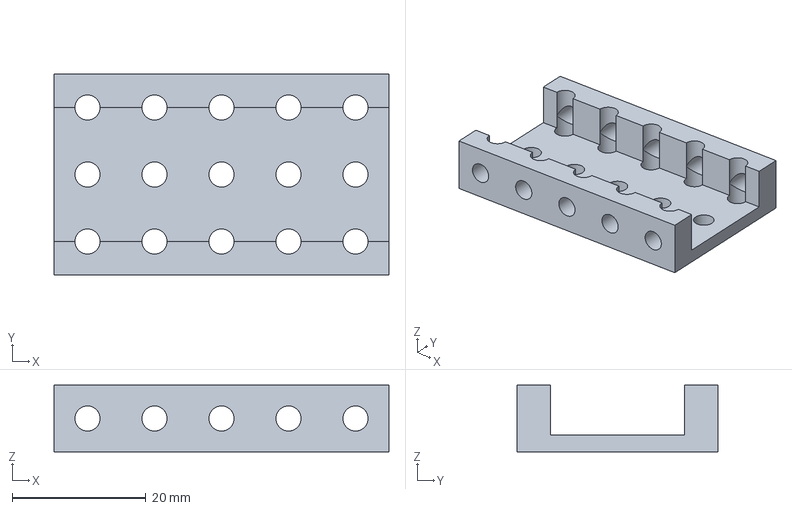
[picture p165: CAD file, 2026-07-30]
model/0215_mini_zeriav/parts/block_U_05_03.step
50.0 x 30.0 x 10.0 mm
