lab-411/Stemfie-X/model/0215_mini_zeriav/parts/base_C_01_13.step

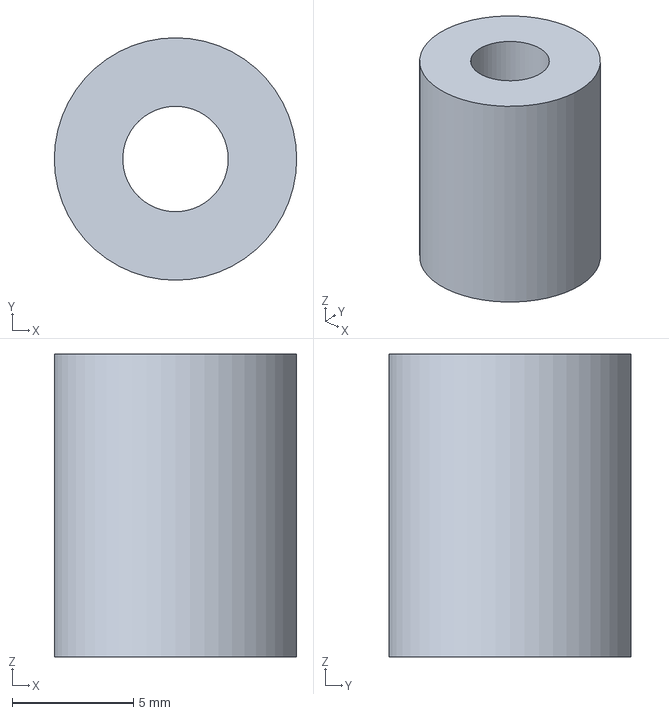
[picture p166: CAD file, 2026-07-30]
model/0215_mini_zeriav/parts/base_C_01_13.step
10.0 x 10.0 x 12.5 mm
