lab-411/Stemfie-X/model/0215_mini_zeriav/parts/block_X_05_04.step

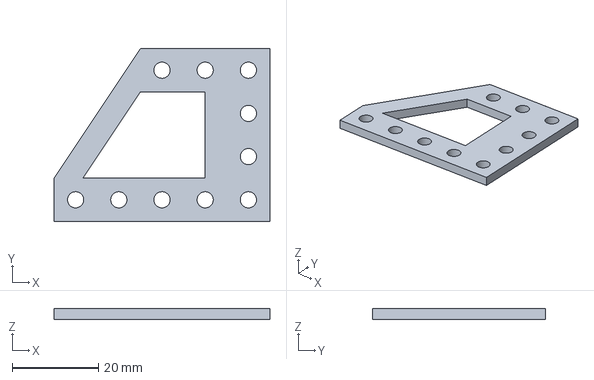
[picture p167: CAD file, 2026-07-30]
model/0215_mini_zeriav/parts/block_X_05_04.step
50.0 x 40.0 x 2.50 mm
