lab-411/Stemfie-X/model/0215_mini_zeriav/parts/axis_3.step

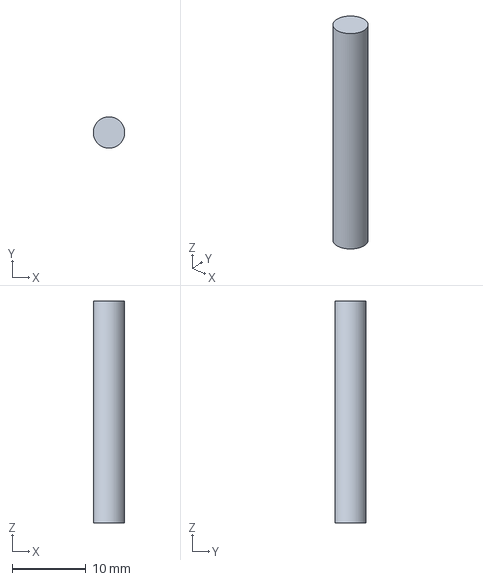
[picture p168: CAD file, 2026-07-30]
model/0215_mini_zeriav/parts/axis_3.step
4.25 x 4.25 x 30.0 mm
