lab-411/Stemfie-X/model/0215_mini_zeriav/parts/brace_B_15.step

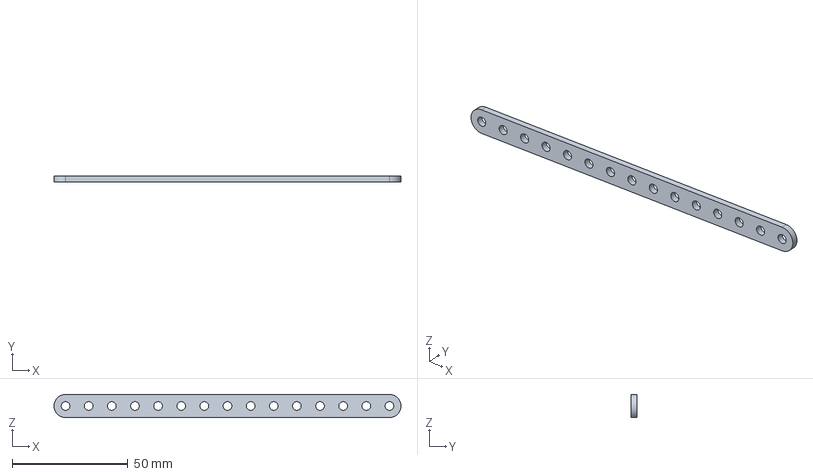
[picture p169: CAD file, 2026-01-02]
model/0215_mini_zeriav/parts/brace_B_15.step
150.0 x 2.50 x 10.0 mm
