lab-411/Stemfie-X/model/0215_mini_zeriav/parts/base_C_01_01.step

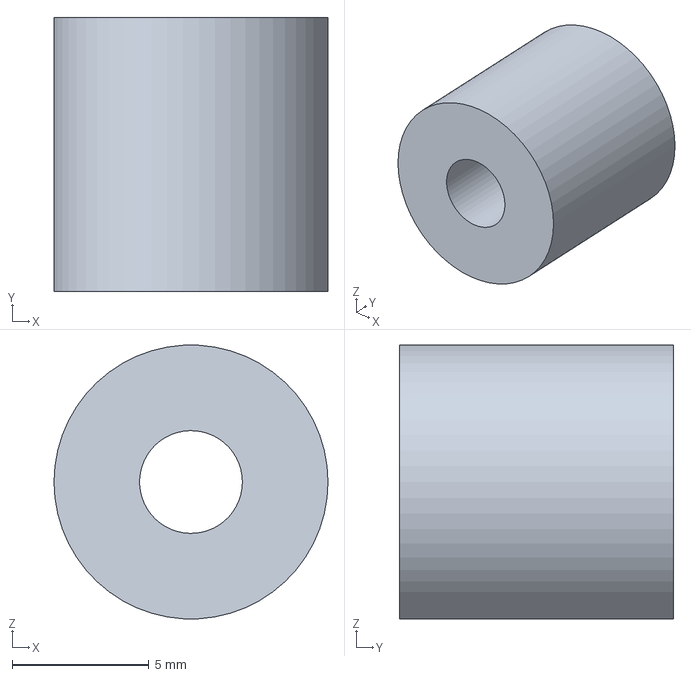
[picture p170: CAD file, 2026-01-02]
model/0215_mini_zeriav/parts/base_C_01_01.step
10.0 x 10.0 x 9.98 mm
