lab-411/Stemfie-X/model/0215_mini_zeriav/parts/comp_C_hook_block_02.step

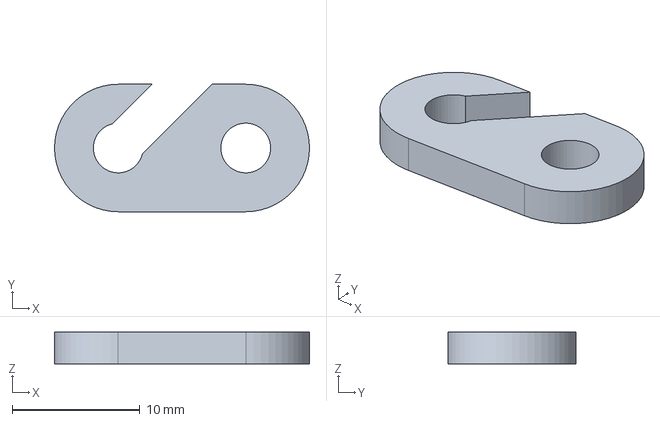
[picture p171: CAD file, 2026-01-02]
model/0215_mini_zeriav/parts/comp_C_hook_block_02.step
20.0 x 10.0 x 2.50 mm
